kvanderlaag/soggy-case/images/Soggy Case rev2 expansion door tabs.png

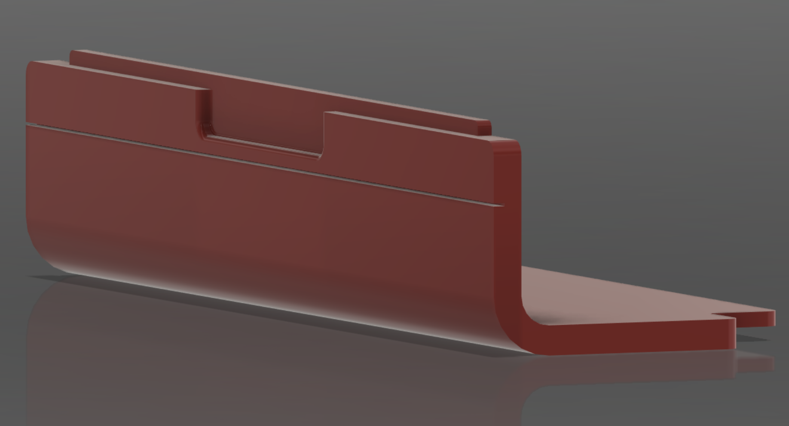
images/Soggy Case rev2 expansion door tabs.png
